chrisjtwomey/canary/include/display/notices/notice-no-firmware.png

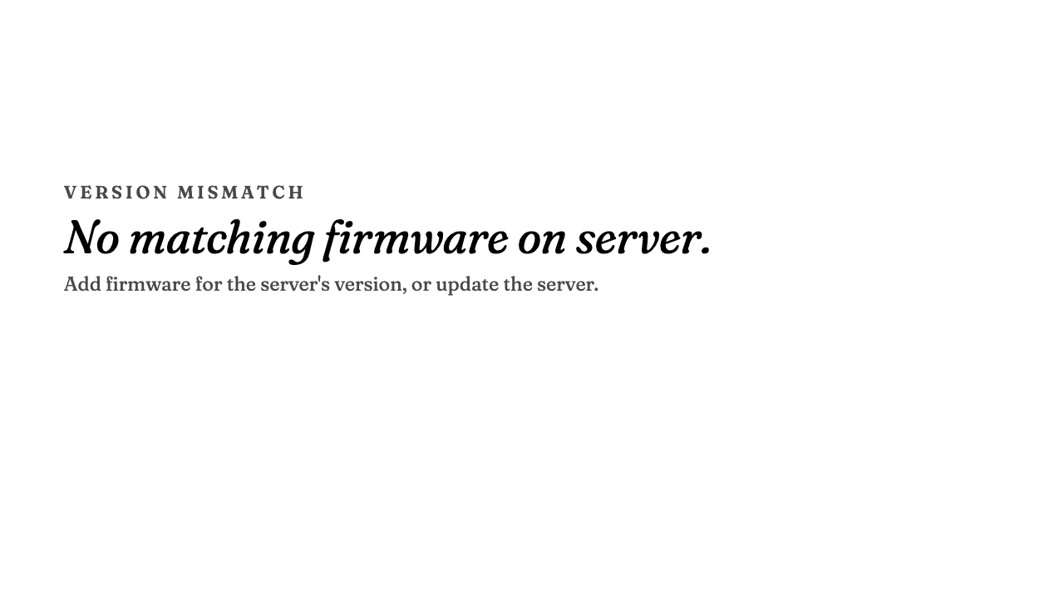
include/display/notices/notice-no-firmware.png
