chrisjtwomey/canary/server/config_page.py

"""config.yaml in the browser: a form in tabs, the file as text, a check, a
save and a restart.

    GET  /web/config     the form, and the file as text in the last tab
    GET  /web/config/export/<store>
                         everything one store holds, a JSON document a line
    POST /web/config/import/<store>
                         such a file back into that store, all of it or none;
                         replace=true puts it over the records that exist
    POST /web/config     mode=form: the form's values written into the file
                         mode=yaml: the text as given
                         mode=restore: config.yaml.bak
                         mode=recalibrate: the dock's SCD41 recalibrated to
                              ppm at its next reading; no action, no restart
                         then action=check: whether that would start the server
                              action=review: the same, and what it changes, as JSON
                              action=save: the same check, then the old file kept
                              as config.yaml.bak, the new one written, and the
                              server restarted on it; as JSON, with the
                              config_version /about names once it runs it

Nothing guards these routes yet: anyone who can reach the server can change
its config.
"""
from __future__ import annotations

import contextlib
import json
import os
import shutil
import time
import zoneinfo
from dataclasses import dataclass, field, replace
from datetime import datetime
from typing import Any, Callable

from airium import Airium
from epd_server.timeranges import MAX_RANGES
from flask import Blueprint, Response, abort, jsonify, redirect, request
from markupsafe import Markup

import config_form as cf
import dock_settings as ds
from about import config_version
from display_settings import DisplaySync
from html_doc import Html
from metrics import RH_BANDS, TEMP_BANDS, VERDICTS
from pages.base import EnvPage
from metrics import age_span
from transfer import Corrupt, Held, Overlap, Transfer
from web import menu_bar, page_head

# The most an imported file may weigh.
MAX_UPLOAD = 64 * 1024 * 1024
# The browse page's URL from /web/config, once the server answers again.
BROWSE_HREF = "./"
YAML_TAB = "yaml"
TAB_NAMES = [t.name for t in cf.TABS] + [YAML_TAB]

# What each drawing on a sheet shows, and how to change it by dragging.
VISUAL_CAPTIONS = {
    "dial": "Each tick is a sync. Hatching marks a time range that is off. "
            "Drag a time range's start to move it.",
    "panel": "Hatching shows where pages are drawn. "
             "Drag the round handle to resize it; click a dot to move it.",
    "slot": "The time before one sync. "
            "Drag the fan band's left edge; past the start, the fan never stops.",
    "start": "Each dot is a reading after the sensor starts; open dots have CO₂ only. "
             "Drag the band's edge to change the warm-up.",
    "comfort": "",
    "disk": "",
    "led": "What the light showed at the dock's last sync, until you change or click a "
           "pattern. Its size follows Brightness.",
}

# What a check or a save that changed nothing says, as a dialog's heading,
# its line, and whether it offers the save. Without scripts the note stays a
# banner.
NOTICES = {
    "No problems found.": ("No problems found", "Save and restart to apply these changes.",
                           True),
    "Nothing to save.": ("No changes", "The file already has these settings.", False),
}

# One wording for the state, whether it is a banner or a refused save.
READ_ONLY = "Cannot save: the server is missing write access to the configuration."


def save(path: str, text: str) -> str:
    """Keep ``path`` as it was beside it, then write ``text`` over it in place.
    Returns what it wrote: ``text`` ending in a newline.

    In place, because a file mounted into a container on its own cannot be
    replaced by a rename.
    """
    shutil.copyfile(path, path + ".bak")
    written = text if text.endswith("\n") else text + "\n"
    with open(path, "w") as f:
        f.write(written)
    return written


@dataclass
class Report:
    """What an import did, shown under the row that did it."""
    store: str = ""
    words: str = ""
    bad: bool = False


@dataclass
class View:
    """What the config page shows."""
    text: str                       # the YAML tab's text
    file_text: str                  # the file as it is
    values: dict[str, Any]          # each field as its input shows it
    initial: dict[str, Any]         # the same from the file: what a change is measured against
    defaults: dict[str, str] = field(default_factory=dict)   # each default, as its input shows it
    errors: dict[str, str] = field(default_factory=dict)
    problem: str = ""
    note: str = ""
    status: str = ""                # the save bar's words, when no note says more
    tab: str = ""                   # the tab to open; empty lets the URL choose
    unreadable: str = ""            # why the form cannot show this file
    held: dict[str, Held] = field(default_factory=dict)      # what each store holds
    now: float = 0.0                # the epoch the store ages are measured to
    disk: tuple[int, int] | None = None     # the stores' disk: total and free bytes
    report: Report = field(default_factory=Report)
    dock: DockState | None = None
    display: dict | None = None     # the display's panel as it reports it: width, height, board
    display_state: DisplayState | None = None
    changes: list[dict] = field(default_factory=list)   # what a check found a save would change


@dataclass
class DockState:
    """What the Dock tab says about the dock beside its settings."""
    applied: bool | None = None     # runs the saved settings; None before it says
    refused: list[str] = field(default_factory=list)
    pending: dict | None = None     # a recalibration it has yet to run
    last: dict | None = None        # its report of the last one it ran
    ppm: str = str(ds.RECALIBRATE_MIN_PPM + 20)
    offline: bool = False           # it has missed two slots; nothing on the tab reaches it
    age_s: int | None = None        # since its last sync
    expired: dict | None = None     # a recalibration that lapsed before the dock ran it
    next_sync: str = ""             # the local time of its next slot, HH:MM
    light: str | None = None        # what its light showed at its last report


def display_panel(entry: dict | None) -> dict | None:
    """The display's panel from its newest report: width, height and board, or
    None before it has said."""
    client = ((entry or {}).get("doc") or {}).get("client") or {}
    panel = client.get("display") or {}
    width, height = panel.get("width"), panel.get("height")
    if not isinstance(width, int) or not isinstance(height, int) or width <= 0 or height <= 0:
        return None
    return {"width": width, "height": height, "board": str(client.get("board") or "")}


@dataclass
class DisplayState:
    """What the Display tab says about the display beside its settings."""
    applied: bool | None = None     # runs the saved settings; None before it reports
    offline: bool = False           # it has missed two slots
    age_s: int | None = None        # since its last sync
    next_sync: str = ""             # the local time of its next slot, HH:MM


def display_state(display: DisplaySync) -> DisplayState:
    offline, age = display.offline()
    return DisplayState(display.applied(), offline, age, display.next_sync())


def dock_state(dock: ds.BoardSettings) -> DockState:
    applied, refused = dock.applied()
    offline, age = dock.offline()
    return DockState(applied, refused, dock.pending(), dock.last_recalibration(),
                     offline=offline, age_s=age, expired=dock.expired(),
                     next_sync=dock.next_sync(), light=dock.light())


def file_view(text: str) -> View:
    try:
        cfg = cf.read(text)
    except cf.FormError as exc:
        values = cf.shown({})
        return View(text, text, values, dict(values), tab=YAML_TAB,
                    unreadable=str(exc))
    values = cf.shown(cfg)
    return View(text, text, values, dict(values), cf.defaults(cfg))


def _id(key: str) -> str:
    return "f-" + key.replace(".", "-")


def _when(t: datetime) -> str:
    return f"{t:%a} {t.day} {t:%b}, {t:%H:%M}"


def _pool_names(view: View) -> list[str]:
    return [n for n, _ in view.values.get("display.pools", []) if n.strip()]


def _pool_row(a: Airium, key: str, name: str, pages: str, images: list[str]) -> None:
    with a.div(klass="row"):
        a.input(type="text", klass="pool-name", name=key + ".name", value=name,
                placeholder="name", spellcheck="false", autocomplete="off",
                **{"aria-label": "Set name"})
        a.input(type="text", klass="chips", name=key + ".pages", value=pages,
                spellcheck="false", autocomplete="off", placeholder="breathe.png, co2-trace.png",
                **{"aria-label": "Pages", "data-options": " ".join(images)})
        a.button(type="button", klass="remove", _t="×", **{"aria-label": "Remove this set"})


# A clock face in the ink of the button it is on.
CLOCK_ICON = Markup('<svg viewBox="0 0 16 16" aria-hidden="true">'
                    '<circle cx="8" cy="8" r="6.25" fill="none" stroke="currentColor" '
                    'stroke-width="1.5"/><path d="M8 4.5V8l2.25 1.5" fill="none" '
                    'stroke="currentColor" stroke-width="1.5" stroke-linecap="round" '
                    'stroke-linejoin="round"/></svg>')


def _time_input(a: Airium, **attrs) -> None:
    """A time input, and the button that opens the page's own picker
    (timepick.js): the browser's takes its colours from the system."""
    lock = {"disabled": "disabled"} if "disabled" in attrs else {}
    with a.span(klass="time"):
        a.input(type="time", **attrs)
        a.button(type="button", klass="pick", _t=CLOCK_ICON,
                 **{"aria-label": "Choose a time", "aria-expanded": "false"}, **lock)


def _clock_row(a: Airium, key: str, start: str, every: str, locked: bool) -> None:
    lock = {"disabled": "disabled"} if locked else {}
    with a.div(klass="row"):
        _time_input(a, name=key + ".from", value=start, **{"aria-label": "From"}, **lock)
        with a.span(klass="every"):
            a.input(type="number", name=key + ".every", value=every, min="0",
                    max=str(24 * 60), step="1", inputmode="numeric",
                    **{"aria-label": "Every, in minutes"}, **lock)
            a.span(klass="unit", _t="min")
        a.button(type="button", klass="remove", _t="×",
                 **{"aria-label": "Remove this time range; the one before takes its hours"},
                 **lock)


def _look_row(a: Airium, key: str, trigger: str, pattern: str, length: str,
              locked: bool) -> None:
    lock = {"disabled": "disabled"} if locked else {}
    with a.div(klass="row"):
        with a.select(name=key + ".trigger", **{"aria-label": "Trigger"}, **lock):
            for t, words in cf.LED_TRIGGER_LABELS.items():
                a.option(value=t, _t=words, **({"selected": "selected"} if t == trigger else {}))
        with a.select(name=key + ".pattern", **{"aria-label": "Pattern"}, **lock):
            for p, words in cf.LED_PATTERN_LABELS.items():
                a.option(value=p, _t=words, **({"selected": "selected"} if p == pattern else {}))
        # Off and solid keep their length, unseen, so each row posts all three.
        with a.span(klass="length idle" if pattern in ds.LED_STILL else "length"):
            a.input(type="number", name=key + ".length_s", value=length,
                    min=f"{ds.led_min_length(pattern):g}", max=f"{ds.LED_LENGTH_MAX_S:g}",
                    step="any", inputmode="decimal", **{"aria-label": "Length, in seconds"},
                    **lock)
            a.span(klass="unit", _t="s")
        a.button(type="button", klass="remove", _t="×",
                 **{"aria-label": "Remove this pattern; its trigger is skipped"}, **lock)


def _row(a: Airium, f: cf.Field, cells: tuple, images: list[str], locked: bool) -> None:
    if f.kind == "pools":
        _pool_row(a, f.key, *cells, images)
    else:
        _look_row(a, f.key, *cells, locked)


# What a new row starts as: a look takes its trigger's default once it has one.
BLANK_ROWS = {"looks": ("", "pulse", "1")}
# The words on each field's button that adds a row.
ADD_WORDS = {"pools": "Add a set", "looks": "Add a pattern"}


def _week(a: Airium, f: cf.Field, view: View, heading: str, locked: bool) -> None:
    """A schedule's groups of days, each with its time ranges. config.js
    shows one group at a time, chosen by its chip, with a toggle for each
    day; without it every group shows under the name of its days. A
    group's inputs are named ``<key>.<n>.``, n its place among the groups."""
    lock = {"disabled": "disabled"} if locked else {}
    with a.fieldset(klass="week", id=_id(f.key),
                    **{"data-key": f.key, "data-initial": cf.initial(view.initial[f.key])}):
        a.legend(klass="name hide" if f.label == heading else "name", _t=f.label)
        # With the rows locked, the key goes unposted and the file's value stands.
        a.input(type="hidden", name=f.key, value="1", **lock)
        a.div(klass="groups", role="group", _t="", **{"aria-label": "Groups of days"})
        for n, (days, rows) in enumerate(view.values.get(f.key, [])):
            prefix = f"{f.key}.{n}"
            chosen = days.split(",")
            with a.div(klass="group"):
                a.p(klass="group-name", _t=cf.days_words(chosen))
                with a.div(klass="days", role="group", **{"aria-label": "Days"}):
                    for d in cf.DAYS:
                        a.button(type="button", _t=cf.DAY_SHORT[d][0], **lock,
                                 **{"data-day": d, "aria-label": cf.DAY_LONG[d],
                                    "aria-pressed": "true" if d in chosen else "false"})
                a.input(type="hidden", name=prefix + ".days", value=days, **lock)
                with a.fieldset(klass="rows clock", **{"data-max": str(MAX_RANGES)}):
                    with a.div(klass="list"):
                        for start, every in rows:
                            _clock_row(a, prefix, start, every, locked)
                    with a.template():
                        _clock_row(a, prefix, "", "", locked)
                    with a.div(klass="foot"):
                        a.button(type="button", klass="add", _t="Add a time range", **lock)
        if f.help:
            a.p(klass="help", _t=f.help)


def _rows(a: Airium, f: cf.Field, view: View, images: list[str], heading: str,
          locked: bool = False) -> None:
    """A field of rows. ``locked`` applies to the Dock tab's rows, the only
    ones on a tab that locks."""
    if f.kind == "week":
        _week(a, f, view, heading, locked)
        return
    rows = view.values.get(f.key, [])
    marks: dict[str, str] = {}
    if f.kind == "looks":
        marks = {"data-looks": json.dumps({t: [p, f"{n:g}"] for t, p, n in ds.LED_LOOKS},
                                          separators=(",", ":")),
                 "data-min": json.dumps({p: f"{ds.led_min_length(p):g}" for p in ds.LED_PATTERNS
                                         if p not in ds.LED_STILL}, separators=(",", ":"))}
    with a.fieldset(klass=f"rows {f.kind}", id=_id(f.key),
                    **{"data-key": f.key, "data-initial": cf.initial(view.initial[f.key])},
                    **marks):
        a.legend(klass="name hide" if f.label == heading else "name", _t=f.label)
        # With the rows locked, the key goes unposted and the file's value stands.
        a.input(type="hidden", name=f.key, value="1", **({"disabled": "disabled"} if locked else {}))
        if f.kind == "looks":
            # The selects and inputs name themselves; these are for the eye.
            with a.div(klass="heads", **{"aria-hidden": "true"}):
                for words in ("Trigger", "Pattern", "Length"):
                    a.span(_t=words)
        with a.div(klass="list"):
            for cells in rows:
                _row(a, f, cells, images, locked)
        with a.template():
            _row(a, f, BLANK_ROWS.get(f.kind, ("", "")), images, locked)
        with a.div(klass="foot"):
            if f.kind in ADD_WORDS:
                a.button(type="button", klass="add", _t=ADD_WORDS[f.kind],
                         **({"disabled": "disabled"} if locked else {}))
            if f.help:
                a.p(klass="help", _t=f.help)


def _control(a: Airium, f: cf.Field, view: View, env: str | None, locked: bool,
             aria_label: str = "") -> None:
    value = view.values.get(f.key, "")
    if env is not None and f.scale != 1 and env.strip().isdigit():
        env = cf.input_text(f, int(env))
    lock = {"disabled": "disabled"} if env is not None or locked else {}
    marks = {"data-default": view.defaults[f.key]} if f.key in view.defaults else {}
    own = {"id": _id(f.key), "name": f.key, "data-key": f.key,
           "data-initial": cf.initial(view.initial.get(f.key, "")), **lock, **marks}
    with a.div(klass="control"):
        if f.kind == "choice":
            chosen = env if env is not None else value
            with a.div(klass="segments", role="radiogroup", id=_id(f.key),
                       **{"aria-labelledby": _id(f.key) + "-name", "data-key": f.key,
                          "data-initial": view.initial.get(f.key, "")}, **marks):
                for choice, words in f.choices:
                    with a.label():
                        a.input(type="radio", name=f.key, value=choice, **lock,
                                **({"checked": "checked"} if choice == chosen else {}))
                        a.span(_t=words)
        elif f.kind == "stops":
            # A slider that moves in the field's stops, with the chosen one's
            # name beside it; config.js keeps the name in step.
            chosen = env if env is not None else value
            words = dict(f.choices)
            a.input(type="range", klass="stops", min="1", max=str(len(f.choices)), step="1",
                    value=chosen, **own,
                    **{"data-words": json.dumps([w for _, w in f.choices], ensure_ascii=False),
                       "aria-valuetext": words.get(str(chosen), "")})
            a.span(klass="unit stop-words", _t=words.get(str(chosen), ""), **{"aria-hidden": "true"})
        elif f.kind in ("bool", "window"):
            on = (env or "").strip().lower() in ("1", "true", "yes", "on") if env is not None \
                else value == "true"
            a.input(type="hidden", name=f.key, value="false", **lock)
            a.input(type="checkbox", klass="switch", value="true", **own,
                    **({"checked": "checked"} if on else {}))
            a.span(klass="state", **{"aria-hidden": "true"})
        else:
            attrs: dict[str, Any] = {"value": env if env is not None else value}
            if aria_label:
                attrs["aria-label"] = aria_label
            if f.hint:
                attrs["placeholder"] = f.hint
            if f.kind in ("int", "number"):
                attrs.update(type="number", step=str(f.step) if f.kind == "int" else "any",
                             inputmode="numeric" if f.kind == "int" else "decimal")
                if f.minimum is not None:
                    attrs["min"] = f"{f.minimum:g}"
                if f.maximum is not None:
                    attrs["max"] = f"{f.maximum:g}"
            elif f.kind != "time":
                attrs.update(type="password" if f.kind == "password" else "text",
                             spellcheck="false", autocomplete="off")
                if f.kind == "zone":
                    attrs["list"] = "zones"
                if f.kind == "order":
                    attrs.update(klass="chips",
                                 **{"data-options": " ".join(_pool_names(view)),
                                    "data-options-from": "display.pools"})
            if f.kind == "time":
                _time_input(a, **own, **attrs)
            else:
                a.input(**own, **attrs)
            if f.unit:
                a.span(klass="unit", _t=f.unit)


def _reset_button(a: Airium, f: cf.Field, view: View) -> None:
    """Puts the default back; it shows once the value differs from it."""
    at_default = view.values.get(f.key) == view.defaults[f.key]
    a.button(type="button", klass="reset", _t="Reset",
             **{"aria-label": f"Reset {f.label}"}, **({"hidden": "hidden"} if at_default else {}))


def _field(a: Airium, f: cf.Field, view: View, images: list[str], heading: str,
           locked: bool = False, sheet: bool = False, by_position: bool = False) -> None:
    """One setting. ``locked`` shows it and keeps it from being changed, as
    an environment variable does, but leaves the file's value standing. On a
    ``sheet`` a dotted leader runs from its name to its value. ``by_position``
    marks a choice the group's position grid stands in for once scripts run."""
    env = f.env_value()
    error = view.errors.get(f.key)
    klass = "field by-position" if by_position else "field"
    if f.kind in cf.ROWS:
        klass += " wide"
    if error:
        klass += " invalid"
    with a.div(klass=klass, **{"data-field": f.key}, **({"data-when": f.when} if f.when else {})):
        if f.kind in cf.ROWS:
            _rows(a, f, view, images, heading, locked)
        else:
            with a.div(klass="head"):
                if f.kind == "choice":
                    a.span(klass="name", id=_id(f.key) + "-name", _t=f.label)
                else:
                    a.label(klass="name", for_=_id(f.key), _t=f.label)
                if f.key in view.defaults and env is None and not locked:
                    _reset_button(a, f, view)
                if f.kind == "password":
                    a.button(type="button", klass="reveal", _t="Show",
                             **{"aria-controls": _id(f.key)})
            if sheet:
                a.span(klass="leader", **{"aria-hidden": "true"})
            _control(a, f, view, env, locked)
        if f.help and f.kind not in cf.ROWS:
            a.p(klass="help", _t=f.help)
        if f.caution:
            # config.js shows it while the value is below data-below.
            shown = f.cautions(env if env is not None else view.values.get(f.key))
            a.p(klass="caution", _t=f.caution,
                **{"data-below": f"{f.recommended:g}"},
                **({"data-zero-means-always": "true"} if f.zero_means_always else {}),
                **({} if shown else {"hidden": "hidden"}))
        if env is not None:
            a.p(klass="env", _t=f"Set by the environment variable {f.env_name}")
        if error:
            a.p(klass="error", id="e-" + _id(f.key)[2:], _t=error)


# The comfort group's fields as ranges: a tab for temperature and one for
# humidity, each with the comfortable range and the acceptable one.
COMFORT_AXES = (("Temperature", "temp", "°C"), ("Humidity", "rh", "%"))
COMFORT_BOXES = (("Comfortable", ""), ("Acceptable", "acceptable_"))


def _comfort_ranges(a: Airium, g: cf.Group, view: View, locked: bool) -> None:
    """Each box's two edges on each axis as one range, under a tab per axis,
    and one reset for all eight. config.js runs the tabs, and shows the reset
    while any edge differs from its default. Without scripts both axes show,
    each under its name."""
    by_key = {f.key: f for f in g.fields}
    with a.div(klass="ranges"):
        with a.div(klass="subtabs", role="tablist", **{"aria-label": "Measurement"}):
            for i, (words, axis, _) in enumerate(COMFORT_AXES):
                a.button(type="button", role="tab", klass="subtab", id=f"comfort-tab-{axis}",
                         _t=words, **{"data-axis": axis, "aria-controls": f"comfort-{axis}",
                                      "aria-selected": "true" if i == 0 else "false"})
        for words, axis, unit in COMFORT_AXES:
            with a.div(klass="range-panel", id=f"comfort-{axis}", role="tabpanel",
                       **{"data-axis": axis, "aria-labelledby": f"comfort-tab-{axis}"}):
                a.p(klass="panel-name", _t=words)
                for box_words, prefix in COMFORT_BOXES:
                    with a.div(klass="range-row"):
                        a.span(klass="name", _t=box_words)
                        with a.div(klass="range"):
                            for n, end in enumerate(("from", "to")):
                                if n:
                                    a.span(klass="dash", _t="–")
                                f = by_key[f"comfort.{prefix}{axis}_{end}"]
                                error = view.errors.get(f.key)
                                with a.div(klass="field" + (" invalid" if error else ""),
                                           **{"data-field": f.key}):
                                    _control(a, replace(f, unit=""), view, f.env_value(), locked,
                                             aria_label=f.label)
                                    if error:
                                        a.p(klass="error", id="e-" + _id(f.key)[2:], _t=error)
                            a.span(klass="unit", _t=unit)
    at_default = all(view.values.get(f.key) == view.defaults.get(f.key) for f in g.fields)
    a.button(type="button", klass="reset-group", _t="Reset to defaults",
             **({"hidden": "hidden"} if at_default or locked else {}))


def _bytes(count: int) -> str:
    """"512 bytes", "64 kB", "3.1 MB", "412 GB": as sheet.js writes them."""
    if count < 1000:
        return f"{count} bytes"
    for unit, size in (("GB", 10**9), ("MB", 10**6)):
        if count >= size:
            n = count / size
            return f"{n:.0f} {unit}" if n >= 100 else f"{n:.1f}".removesuffix(".0") + f" {unit}"
    return f"{count / 1000:.0f} kB"


def _since(oldest: float, now: float) -> str:
    """"since 09:14" today, "since 3 Sep" this year, "since 3 Sep 2025" before."""
    t, today = datetime.fromtimestamp(oldest), datetime.fromtimestamp(now)
    if t.date() == today.date():
        return f"since {t:%H:%M}"
    return f"since {t.day} {t:%b}" + ("" if t.year == today.year else f" {t.year}")


def _contents_parts(held: Held, now: float) -> list[str]:
    """["48,210 records", "3.1 MB", "since 3 Sep"], or that there are none."""
    if not held.records:
        return ["No records yet."]
    parts = [f"{held.records:,} record{'' if held.records == 1 else 's'}", _bytes(held.size)]
    if held.oldest is not None:
        parts.append(_since(held.oldest, now))
    return parts


def _contents(a: Airium, store: str, view: View) -> None:
    """What the store's file holds, as a line of the sheet."""
    with a.div(klass="field contents", **{"data-contents": store}):
        with a.div(klass="head"):
            a.span(klass="name", _t="Contents")
        a.span(klass="leader", **{"aria-hidden": "true"})
        with a.div(klass="control"):
            # Each part in a span of its own, so a line breaks between them.
            with a.span(klass="value"):
                for i, part in enumerate(_contents_parts(view.held[store], view.now)):
                    if i:
                        a(" · ")
                    a.span(_t=part)


def _transfer(a: Airium, store: str, held: Held, report: Report) -> None:
    """The store's file out and back in, as two links under its heading;
    Download shows once the store holds a record. Upload's controls belong
    to the form beside the settings form, because a form cannot hold
    another. config.js hides the file input and Replace, and asks instead."""
    form = f"import-{store}"
    with a.div(klass="transfer", **{"data-import": store}):
        with a.p(klass="links"):
            a.a(klass="link", href=f"config/export/{store}", download="download",
                _t="Download", **{"data-export": store},
                **({} if held.records else {"hidden": "hidden"}))
            a.button(type="submit", klass="link", form=form, _t="Upload")
        with a.p(klass="pick"):
            a.input(type="file", id=f"file-{store}", name="file", form=form,
                    accept=".jsonl,application/x-ndjson", **{"aria-label": "File to upload"})
            with a.label(klass="over"):
                a.input(type="checkbox", name="replace", value="true", form=form)
                a.span(_t="Replace")
        if report.store == store:
            a.p(klass="report error" if report.bad else "report help", _t=report.words)


# Each store's name, as its group on the Storage tab heads it, in the tab's order.
STORE_NAMES = {g.store: g.heading for t in cf.TABS for g in t.groups if g.store}


def _disk_usage(stores: dict[str, Transfer]) -> tuple[int, int] | None:
    """The total and free bytes of the disk the first store's file is on;
    None without stores, or when the disk cannot be read."""
    for store in stores.values():
        try:
            usage = shutil.disk_usage(os.path.dirname(os.path.abspath(store.path)))
        except OSError:
            return None
        return usage.total, usage.free
    return None


def _disk_data(held: dict[str, Held], disk: tuple[int, int] | None) -> dict:
    """What the disk drawing draws: each store's name and bytes, and the
    disk's total and free bytes when they are known."""
    data: dict[str, Any] = {"stores": [{"name": name, "size": held[store].size}
                                       for store, name in STORE_NAMES.items() if store in held]}
    if disk is not None:
        data["total"], data["free"] = disk
    return data


# When each board takes new settings: the dock before the reading at its
# sync, the display in the answer to its sync.
TAKES = {"dock": "before its next sync", "display": "when it next syncs"}


def _settings_line(a: Airium, state: DockState | DisplayState, board: str) -> None:
    """Whether ``board`` runs the saved settings, as a banner across its tab:
    a pill naming the state, then what it means. config.js puts a new one in
    its place from GET /web/config/live."""
    last = Markup("Last sync {} ago.").format(age_span(state.age_s or 0))
    at = f", at {state.next_sync}" if state.next_sync else ""
    if state.offline and board == "dock":
        pill = ("offline", "Offline", last + " Settings unlock when the dock syncs again.")
    elif state.offline:
        pill = ("offline", "Offline", last + (" The display takes these settings when it "
                                              "syncs again." if state.applied is False else ""))
    elif state.applied is None:
        pill = None
    elif state.applied:
        pill = ("synced", "Synchronized", last)
    else:
        pill = ("waiting", "Not synchronized",
                f"The {board} takes these settings {TAKES[board]}{at}.")
    with a.div(klass="board-state", id=f"{board}-state",
               **{"data-offline": "true" if state.offline else "false"}):
        with a.p(klass="banner board-line", id=f"{board}-applied"):
            if pill is None:
                a.span(_t=f"No sync from the {board} yet. Settings apply once it connects.")
            else:
                klass, name, words = pill
                a.span(klass=f"pill {klass}", id=f"{board}-{klass}", _t=name)
                a.span(_t=words)
        if getattr(state, "refused", None):
            names = ", ".join(_label_of(("dock", *key.split("."))) for key in state.refused)
            a.p(klass="error", id="dock-refused",
                _t=f"Refused by the dock: {names}. Check the dock's firmware version.")


def _saved_words(states: dict[str, DockState | DisplayState | None]) -> str:
    """The save bar's words after a save: which board has yet to take the new
    settings, and when."""
    waiting = [(board, _takes_at(state)) for board, state in states.items()
               if state is not None and state.applied is False]
    if not waiting:
        return "Saved."
    (board, when), *rest = waiting
    return (f"Saved. The {board} takes the new settings {when}"
            + "".join(f", the {b} {w}" for b, w in rest) + ".")


def _takes_at(state: DockState | DisplayState) -> str:
    if state.offline:
        return "when it syncs again"
    return f"at {state.next_sync}" if state.next_sync else "at its next sync"


def _label_of(path: tuple) -> str:
    """A setting's name as its own tab shows it."""
    f = cf.field_at(path)
    return (f.long or f.label) if f else ".".join(path)


def _recalibration_words(state: DockState) -> str:
    if state.pending:
        asked = datetime.fromtimestamp(state.pending["id"])
        lapses = datetime.fromtimestamp(state.pending["id"] + ds.RECALIBRATE_WITHIN_S)
        return (f"Waiting for the dock's next sync: {state.pending['ppm']} ppm, "
                f"asked {_when(asked)}. Expires at {lapses:%H:%M}.")
    if state.expired:
        return (f"Recalibration to {state.expired['ppm']} ppm expired: "
                "the dock did not sync within an hour.")
    last = state.last
    if not last:
        return ("Keep the dock in air of a known CO₂ level for 3 minutes, then enter that level. "
                "Outdoor air is about 420 ppm.")
    asked = _when(datetime.fromtimestamp(last["id"]))
    if not last.get("ok"):
        return (f"Last recalibration failed: {last.get('ppm', '?')} ppm, asked {asked}. "
                "The sensor refused it. Try again after 3 minutes in that air.")
    correction = last.get("correction_ppm", 0)
    return (f"Last recalibration: {last.get('ppm', '?')} ppm, asked {asked}. "
            f"Corrected by {correction:+d} ppm.")


def _recalibrate(a: Airium, state: DockState, report: Report, sheet: bool = False) -> None:
    """The row that asks for a recalibration. Its controls belong to the form
    beside the settings form, as the import rows' do."""
    form = "recalibrate-form"
    lock = {"disabled": "disabled"} if state.offline else {}
    with a.div(klass="field wide", **{"data-recalibrate": "scd41"}):
        with a.div(klass="head"):
            a.label(klass="name", for_="recalibrate-ppm", _t="Recalibrate")
        if sheet:
            a.span(klass="leader", **{"aria-hidden": "true"})
        with a.div(klass="control"):
            a.input(type="number", id="recalibrate-ppm", name="ppm", form=form,
                    value=state.ppm, step="1", inputmode="numeric",
                    min=str(ds.RECALIBRATE_MIN_PPM), max=str(ds.RECALIBRATE_MAX_PPM), **lock)
            a.span(klass="unit", _t="ppm")
            a.button(type="submit", klass="button", form=form, _t="Recalibrate", **lock)
        if report.store == "recalibrate":
            a.p(klass="error" if report.bad else "help", _t=report.words)
        else:
            a.p(klass="help", id="recalibrate-state", _t=_recalibration_words(state))


def _changes_table(a: Airium, changes: list[dict]) -> None:
    """Each change as its setting, what it was and what it becomes."""
    with a.div(klass="changes-box"):
        with a.table(klass="changes"):
            with a.tbody():
                for c in changes:
                    with a.tr():
                        a.th(_t=c["name"])
                        a.td(klass="old", _t=c["old"])
                        a.td(klass="to", _t="→")
                        a.td(klass="new", _t=c["new"])


def _savebar(a: Airium, writable: bool, status: str, *, discard: bool) -> None:
    with a.footer(klass="savebar"):
        a.p(klass="status", _t=status, **{"aria-live": "polite",
                                          "data-idle": "No changes."})
        with a.div(klass="choice"):
            if discard:
                a.a(klass="button discard", href="config", _t="Discard")
            a.button(type="submit", name="action", value="check", _t="Check")
            a.button(type="submit", name="action", value="save", klass="primary",
                     _t="Save and restart", **({} if writable else {"disabled": "disabled"}))


@contextlib.contextmanager
def _nothing():
    yield


def _place_words(x: str, y: str) -> str:
    """"Top left", "Centre right", "Centre": a grid square's name."""
    across = {"left": "left", "center": "centre", "right": "right"}[x]
    down = {"top": "Top", "center": "Centre", "bottom": "Bottom"}[y]
    return "Centre" if x == y == "center" else f"{down} {across}"


def _position(a: Airium, g: cf.Group, view: View, locked: bool) -> None:
    """A 3 × 3 grid that sets the group's two alignments, across and up and
    down, with one click. It stands in for their two rows of choices, which
    stay in the form as what a save sends."""
    across, down = [f for f in g.fields if f.kind == "choice"]
    x = view.values.get(across.key) or "center"
    y = view.values.get(down.key) or "center"
    lock = {"disabled": "disabled"} if locked or across.env_value() or down.env_value() else {}
    with a.div(klass="field position"):
        with a.div(klass="head"):
            a.span(klass="name", id="position-name", _t="Position")
        a.span(klass="leader", **{"aria-hidden": "true"})
        with a.div(klass="control"):
            with a.div(klass="grid3", role="group",
                       **{"aria-labelledby": "position-name", "data-x": across.key,
                          "data-y": down.key}):
                for yv in ("top", "center", "bottom"):
                    for xv in ("left", "center", "right"):
                        a.button(type="button", _t="", **lock,
                                 **{"data-x": xv, "data-y": yv,
                                    "aria-label": _place_words(xv, yv),
                                    "aria-pressed": "true" if (xv, yv) == (x, y) else "false"})


def _display_size(a: Airium, view: View) -> None:
    """The size the display reports, against the saved one."""
    display = view.display
    if not display:
        return
    said = f"{display['width']} × {display['height']} px"
    if display.get("board"):
        said += f", {display['board']}"
    try:
        saved = (int(view.initial["image.width"]), int(view.initial["image.height"]))
    except (KeyError, ValueError):
        saved = None
    if saved == (display["width"], display["height"]):
        a.p(klass="help display-size", id="display-size", _t=f"The display reports {said}.")
    else:
        a.p(klass="error display-size", id="display-size",
            _t=f"Size mismatch: the display reports {said}. Set Width and Height to match.")


def _runs(fields: tuple[cf.Field, ...], sheet: bool) -> list[tuple[str, list[cf.Field]]]:
    """The fields in order, those in a row that show only while another field
    holds a value run together under that ``when``, on a sheet, so two or
    more can share one box. Elsewhere each field stands alone."""
    runs: list[tuple[str, list[cf.Field]]] = []
    for f in fields:
        when = f.when if sheet else ""
        if when and runs and runs[-1][0] == when:
            runs[-1][1].append(f)
        else:
            runs.append((when, [f]))
    return runs


def _group(a: Airium, g: cf.Group, view: View, images: list[str], locked: bool,
           sheet: bool = False) -> None:
    """A group's heading, the line under it that says what the group is for,
    and its fields. On a ``sheet`` a heading such as "CO₂ · SCD41" takes two
    lines, the part under the measurement, the heading and its line keep to
    their column, and the group's drawing, when it has one, comes before its
    fields."""
    stored = g.store in view.held
    with a.div(klass="heading") if sheet else _nothing():
        if g.heading and sheet and " · " in g.heading:
            title, part = g.heading.split(" · ", 1)
            with a.h2(klass="group label"):
                a.span(_t=title)
                a.span(klass="part", _t=part)
        elif g.heading:
            a.h2(klass="group label", _t=g.heading)
        if g.heading and g.about:
            a.p(klass="about", _t=g.about)
        if stored:
            _transfer(a, g.store, view.held[g.store], view.report)
    with a.div(klass=f"content visual-{g.visual}" if g.visual else "content") if sheet \
            else _nothing():
        if sheet and g.visual:
            # A dial draws the schedule its group holds.
            key = next((f.key for f in g.fields if f.kind == "week"), "")
            marks = {"data-schedule": key} if key else {}
            rec = next((f.recommended for f in g.fields if f.recommended is not None), None)
            if rec is not None:
                marks["data-recommended"] = f"{rec:g}"
            if g.visual == "disk":
                marks["data-disk"] = json.dumps(_disk_data(view.held, view.disk),
                                                separators=(",", ":"))
            if g.visual == "comfort":
                # The Comfort page's sentences, so the live text says what it would.
                marks["data-verdicts"] = json.dumps(
                    {"temp": TEMP_BANDS, "rh": RH_BANDS, "words": VERDICTS},
                    separators=(",", ":"))
            with a.div(klass="visual"):
                if g.visual == "led":
                    # A dot sheet.js lights as the dock would, and the look it plays:
                    # what the light showed at the dock's last report, until a row is picked.
                    light = view.dock.light if view.dock and not view.dock.offline else None
                    with a.div(klass="led-preview", id="visual-led", **{"data-visual": "led"},
                               **({"data-light": light} if light else {})):
                        a.span(klass="dot", **{"aria-hidden": "true"})
                        a.span(klass="led-look", _t="", **{"aria-live": "polite"})
                else:
                    a.canvas(id="-".join(["visual", g.visual, *key.split(".")]) if key
                             else f"visual-{g.visual}",
                             **{"data-visual": g.visual, "aria-hidden": "true"}, **marks)
                    if g.visual == "comfort":
                        # The room now, and its words with the boxes as drawn; sheet.js fills it.
                        with a.div(klass="comfort-now", id="comfort-now", **{"aria-live": "polite"}):
                            with a.div(klass="now-line"):
                                a.span(klass="now-temp", _t="—")
                                a.span(klass="unit", _t="°C")
                            with a.div(klass="now-line"):
                                a.span(klass="now-rh", _t="—")
                                a.span(klass="unit", _t="%")
                            a.div(klass="verdict", _t="")
                caption = g.caption or VISUAL_CAPTIONS[g.visual]
                if caption:
                    a.p(klass="caption", _t=caption)
        with a.div(klass="fields"):
            if stored:
                _contents(a, g.store, view)
            if g.visual == "comfort":
                _comfort_ranges(a, g, view, locked)
            for when, fields in [] if g.visual == "comfort" else _runs(g.fields, sheet):
                boxed = when and len(fields) > 1
                with a.div(klass="subsection", **{"data-when": when}) if boxed else _nothing():
                    for f in fields:
                        _field(a, f, view, images, g.heading, locked, sheet,
                               by_position=g.action == "position" and f.kind == "choice")
            if g.action == "position":
                _position(a, g, view, locked)
            if g.action == "display":
                _display_size(a, view)
            if g.action == "recalibrate" and view.dock is not None:
                _recalibrate(a, view.dock, view.report, sheet)


def _tab_problems(view: View) -> set[str]:
    tabs = {cf.TAB_OF[k] for k in view.errors if k in cf.TAB_OF}
    if view.problem and view.tab and view.tab != YAML_TAB:
        tabs.add(view.tab)
    return tabs


def config_html(pages: list[EnvPage], view: View, writable: bool,
                bak: datetime | None = None) -> str:
    images = [p.png_filename for p in pages]
    tabs = [] if view.unreadable else [(t.name, t.title) for t in cf.TABS]
    tabs.append((YAML_TAB, "YAML"))
    marked = _tab_problems(view)
    status = view.note or view.status or (
        "Not saved. Fix the marked fields." if view.errors
        else "Not saved." if view.problem else "No changes.")
    a = Html()
    a("<!DOCTYPE html>")
    with a.html(lang="en"):
        page_head(a, "Canary · Settings")
        with a.body(klass="web config"):
            menu_bar(a, pages, BROWSE_HREF, "config")
            with a.main(klass="settings"):
                with a.div(klass="top"):
                    a.h1(klass="title label", _t="Settings")
                    with a.div(klass="where"):
                        if bak is not None and writable:
                            with a.form(method="post", action="config", klass="restore",
                                        id="restore-form",
                                        **{"data-title": "Restore the previous version?",
                                           "data-confirm": "Restore and restart"}):
                                a.input(type="hidden", name="mode", value="restore")
                                a.span(klass="stamp", _t=f"Last saved {_when(bak)}")
                                a.button(type="submit", name="action", value="save",
                                         klass="link", _t="Restore")
                with a.nav(klass="tabs", role="tablist", **{"aria-label": "Sections"},
                           **({"data-open": view.tab} if view.tab else {})):
                    for name, title in tabs:
                        a.a(href=f"#{name}", id=f"tab-{name}", role="tab",
                            klass="tab problem" if name in marked else "tab",
                            _t=title, **{"data-tab": name, "aria-controls": f"panel-{name}"})
                if not writable:
                    a.p(klass="banner", id="read-only",
                        _t=READ_ONLY)
                if view.unreadable:
                    a.p(klass="banner problem", id="unreadable", _t=view.unreadable)
                if view.problem:
                    a.p(klass="banner problem", id="problem", _t=f"Not saved: {view.problem}")
                if view.note:
                    a.p(klass="banner", id="note", _t=view.note)
                if not view.unreadable:
                    with a.form(method="post", action="config", id="settings-form",
                                novalidate="novalidate",
                                **{"data-title": "Save and restart?",
                                   "data-confirm": "Save and restart"}):
                        a.input(type="hidden", name="mode", value="form")
                        a.input(type="hidden", name="tab", value=view.tab or cf.TABS[0].name)
                        for t in cf.TABS:
                            with a.section(klass="panel sheet" if t.sheet else "panel",
                                           id=f"panel-{t.name}", role="tabpanel",
                                           **{"data-tab": t.name,
                                              "aria-labelledby": f"tab-{t.name}"}):
                                locked = False
                                if t.name == "dock" and view.dock is not None:
                                    _settings_line(a, view.dock, "dock")
                                    locked = view.dock.offline
                                if t.name == "display" and view.display_state is not None:
                                    _settings_line(a, view.display_state, "display")
                                for g in t.groups:
                                    if t.sheet:
                                        with a.div(klass="section"):
                                            _group(a, g, view, images, locked, sheet=True)
                                    else:
                                        _group(a, g, view, images, locked)
                        _savebar(a, writable, status, discard=True)
                    for store in view.held:
                        a.form(method="post", action=f"config/import/{store}",
                               enctype="multipart/form-data", id=f"import-{store}")
                    if view.dock is not None:
                        with a.form(method="post", action="config", id="recalibrate-form"):
                            a.input(type="hidden", name="mode", value="recalibrate")
                with a.form(method="post", action="config", id="yaml-form",
                            **{"data-title": "Save and restart?",
                               "data-confirm": "Save and restart"}):
                    a.input(type="hidden", name="mode", value="yaml")
                    a.input(type="hidden", name="tab", value=YAML_TAB)
                    with a.section(klass="panel", id=f"panel-{YAML_TAB}", role="tabpanel",
                                   **{"data-tab": YAML_TAB, "aria-labelledby": f"tab-{YAML_TAB}"}):
                        a.textarea(name="text", rows="24", spellcheck="false", _t=view.text,
                                   **{"aria-label": "config.yaml", "data-key": "text",
                                      "data-initial": view.file_text})
                        _savebar(a, writable, status, discard=True)
            with a.dialog(id="review", **{"aria-labelledby": "review-title"}):
                with a.form(method="dialog"):
                    a.h2(klass="label", id="review-title", _t="Save and restart?")
                    a.p(klass="lead", id="review-lead")
                    with a.div(klass="changes-box"):
                        with a.table(klass="changes"):
                            a.tbody(id="review-list", _t="")
                    with a.div(klass="choice"):
                        a.button(value="cancel", _t="Cancel")
                        a.button(value="confirm", klass="primary", id="review-confirm",
                                 _t="Save and restart")
            if view.note in NOTICES:
                title, lead, offers_save = NOTICES[view.note]
                with a.dialog(id="notice", **{"aria-labelledby": "notice-title"},
                              **({"klass": "with-changes"} if view.changes else {})):
                    with a.form(method="dialog"):
                        a.h2(klass="label", id="notice-title", _t=title)
                        a.p(klass="lead", _t=lead)
                        if view.changes:
                            _changes_table(a, view.changes)
                        with a.div(klass="choice"):
                            a.button(value="close", autofocus="autofocus", _t="Close",
                                     **({} if offers_save else {"klass": "primary"}))
                            if offers_save:
                                a.button(value="save", klass="primary", _t="Save and restart",
                                         **({} if writable else {"disabled": "disabled"}))
            with a.datalist(id="zones"):
                for zone in sorted(zoneinfo.available_timezones()):
                    a.option(value=zone)
            a.script(src="rough.iife.min.js")
            a.script(src="config.js")
            a.script(src="timepick.js")
            a.script(src="sheet.js")
            a.script(src="ago.js")
    return str(a)


def restarting_html(pages: list[EnvPage], tab: str) -> str:
    """The page a save without config.js gets: it opens the config page
    again after a minute, once the server is back."""
    a = Html()
    a("<!DOCTYPE html>")
    with a.html(lang="en"):
        page_head(a, "Canary · Restarting", refresh=f"60; url=config?saved=1#{tab}")
        with a.body(klass="web config"):
            menu_bar(a, pages, BROWSE_HREF, "config")
            with a.main(klass="settings"):
                a.h1(klass="title label", _t="Settings")
                a.p(klass="banner", id="restarting", _t="Restarting…")
    return str(a)


def config_blueprint(pages: list[EnvPage], path: str, check: Callable[[str], None],
                     restart: Callable[[], None],
                     stores: dict[str, Transfer] | None = None,
                     dock: ds.BoardSettings | None = None,
                     display: DisplaySync | None = None,
                     boards: Callable[[str], dict | None] | None = None,
                     take_network: Callable[[str], None] | None = None) -> Blueprint:
    """The /web/config routes for the file at ``path``.

    Args:
        check: raises ValueError, with the problem, unless the text would
            start the server.
        restart: restarts the server once the response has gone out.
        stores: the store behind each group of the Storage tab that a file
            can come out of and go into, by the group's ``store`` name.
        dock: the dock's settings, for what the Dock tab says of them and
            for its recalibration.
        display: whether the display runs the saved settings, for what the
            Display tab says of them.
        boards: what the server knows of a board, as DeviceReports.device
            gives it, for the size the display reports.
        take_network: takes a saved file whose changes are all to the
            install page's settings, in place of a restart: they change only
            what an install writes, so the server can take them as it runs.
    """
    bp = Blueprint("config", __name__, url_prefix="/web/config")
    stores = stores or {}

    @bp.record_once
    def cap_uploads(state):
        state.app.config.setdefault("MAX_CONTENT_LENGTH", MAX_UPLOAD)

    def writable() -> bool:
        return os.access(path, os.W_OK)

    def bak() -> datetime | None:
        try:
            return datetime.fromtimestamp(os.path.getmtime(path + ".bak"))
        except OSError:
            return None

    def board_states(view: View) -> None:
        if dock is not None and view.dock is None:
            view.dock = dock_state(dock)
        if display is not None and view.display_state is None:
            view.display_state = display_state(display)

    def page(view: View, status: int = 200):
        view.held = {name: store.held() for name, store in stores.items()}
        view.now = time.time()
        view.disk = _disk_usage(stores)
        board_states(view)
        if boards is not None:
            view.display = display_panel(boards("canary-display"))
        return config_html(pages, view, writable(), bak()), status

    @bp.route("/live", methods=["GET"])
    def live():
        """The Dock and Display tabs' lines about each board as it is now,
        for config.js."""
        if dock is None and display is None:
            abort(404)
        answer: dict[str, Any] = {}
        if dock is not None:
            state = dock_state(dock)
            a = Html()
            _settings_line(a, state, "dock")
            answer.update(state=str(a), recalibration=_recalibration_words(state),
                          offline=state.offline, light=state.light)
        if display is not None:
            a = Html()
            _settings_line(a, display_state(display), "display")
            answer["display"] = str(a)
        return jsonify(answer)

    @bp.route("/export/<name>", methods=["GET"])
    def export(name: str):
        store = stores.get(name)
        if store is None:
            abort(404)
        stamp = datetime.now().strftime("%Y%m%d")
        return Response(store.lines(), mimetype="application/x-ndjson", headers={
            "Content-Disposition": f'attachment; filename="{name}-{stamp}.jsonl"'})

    @bp.route("/import/<name>", methods=["POST"])
    def bring_in(name: str):
        store = stores.get(name)
        if store is None:
            abort(404)
        as_json = "application/json" in request.headers.get("Accept", "")

        def answer(words: str, status: int = 200, bad: bool = False, advice: str = "",
                   **counts):
            """The answer as JSON, or the page with it under the import row.
            ``advice`` is for the page alone: with config.js a dialog asks."""
            if as_json:
                return jsonify(words=words, bad=bad, **counts), status
            with open(path) as f:
                view = file_view(f.read())
            view.tab = "storage"
            view.report = Report(name, " ".join(filter(None, (words, advice))), bad)
            return page(view, status)

        upload = request.files.get("file")
        if upload is None or not upload.filename:
            return answer("Choose a file to upload.", 400, bad=True)
        try:
            counts = store.take(upload.stream, request.form.get("replace") == "true")
        except Corrupt as exc:
            return answer(f"Upload failed: line {exc.line} is not a record. Check the file.",
                          400, bad=True)
        except Overlap as exc:
            return answer(f"{exc.held:,} of {exc.total:,} records already exist.",
                          409, bad=True, held=exc.held, total=exc.total,
                          advice="Tick Replace and choose the file again.")
        except FileNotFoundError:
            return answer("This server does not keep those records.", 404, bad=True)
        held = {n: s.held() for n, s in stores.items()}
        words = f"Added {counts['added']:,} of {counts['total']:,} records."
        if counts["held"]:
            words += f" {counts['held']:,} replaced."
        return answer(words, contents=_contents_parts(held[name], time.time()),
                      records=held[name].records, disk=_disk_data(held, _disk_usage(stores)),
                      **counts)

    @bp.errorhandler(413)
    def too_big(exc):
        words = f"File too big. Choose one under {MAX_UPLOAD // (1024 * 1024)} MB."
        if "application/json" in request.headers.get("Accept", ""):
            return jsonify(words=words, bad=True), 413
        with open(path) as f:
            view = file_view(f.read())
        view.tab = "storage"
        view.report = Report((request.view_args or {}).get("name", ""), words, True)
        return page(view, 413)

    @bp.route("", methods=["GET"])
    def show():
        with open(path) as f:
            view = file_view(f.read())
        if request.args.get("saved"):
            board_states(view)
            view.status = _saved_words({"dock": view.dock, "display": view.display_state})
        return page(view)

    @bp.route("", methods=["POST"])
    def change():
        form = request.form
        mode = form.get("mode") or ("yaml" if "text" in form else "form")
        action = form.get("action", "check")
        with open(path) as f:
            current = f.read()
        view = file_view(current)
        view.tab = form.get("tab", "") if form.get("tab") in TAB_NAMES else ""

        wants_json = action == "review" or "application/json" in request.headers.get("Accept", "")

        def refuse(problem: str, status: int = 400, key: str | None = None):
            if wants_json:
                at = {"field": key, "error": view.errors[key]} if key in view.errors else {}
                return jsonify(problem=problem, **at), status
            view.problem = problem
            return page(view, status)

        if mode == "recalibrate":
            if dock is None:
                abort(404)
            ppm = form.get("ppm", "")
            try:
                dock.recalibrate(ppm)
            except ValueError as exc:
                view.tab = "dock"
                view.dock = dock_state(dock)
                view.dock.ppm = ppm
                view.report = Report("recalibrate", str(exc), True)
                return page(view, 400)
            return redirect("config#dock", 303)

        if mode == "restore":
            try:
                with open(path + ".bak") as f:
                    text = f.read()
            except OSError:
                return refuse("No earlier version to restore.", 404)
        elif mode == "yaml":
            # A text box sends its lines with CRLF.
            text = form.get("text", "").replace("\r\n", "\n")
            view.text, view.tab = text, YAML_TAB
        else:
            view.values.update(cf.submitted(form))
            try:
                edit = cf.apply(current, form)
            except cf.FormError as exc:
                return refuse(str(exc))
            if edit.errors:
                view.errors = edit.errors
                key = next(f.key for f in cf.FIELDS if f.key in edit.errors)
                view.tab = cf.TAB_OF.get(key, view.tab)
                return refuse(f"{cf.name_of(cf.BY_KEY[key].path)}: {edit.errors[key]}", key=key)
            text = edit.text

        try:
            check(text)
        except ValueError as exc:
            problem = str(exc)
            if mode == "form":
                key, tab = cf.locate(problem)
                if key:
                    f = cf.BY_KEY[key]
                    if f.refused:
                        problem = f"{cf.name_of(f.path)}: {f.refused}"
                    view.errors[key] = f.refused or problem
                view.tab = tab or view.tab
                return refuse(problem, key=key)
            return refuse(problem)

        if action == "review":
            return jsonify(changes=cf.changes(cf.read(current), cf.read(text)),
                           same=text == current)
        if action != "save":
            if text == current:
                view.note = "Nothing to save."
            else:
                view.note = "No problems found."
                view.changes = cf.changes(cf.read(current), cf.read(text))
            return page(view)
        if text == current:
            if wants_json:
                return jsonify(saved=False, same=True)
            view.note = "Nothing to save."
            return page(view)
        if not writable():
            return refuse(READ_ONLY, 403)
        try:
            written = save(path, text)
        except OSError as exc:
            return refuse(f"Save failed: {exc.strerror}.", 500)
        if take_network is not None and mode == "form" and set(edit.changed) <= cf.INSTALL_KEYS:
            take_network(written)
            if wants_json:
                return jsonify(saved=True, config=config_version(written), restarted=False)
            return redirect("install", 303)
        restart()
        if wants_json:
            return jsonify(saved=True, config=config_version(written))
        return restarting_html(pages, view.tab or cf.TABS[0].name)

    return bp
