chrisjtwomey/canary/src/splash.cpp

#include "display/Splash.h"

#include <Arduino.h>

#include "epd.h"
#include "display/Notice.h"
#include "display/ProgressBar.h"
#include "display/fonts/FrauncesDetail.h"
#include "display/fonts/FrauncesDetailItalic.h"
#include "log_utils.h"
#include "version.h"

// The splash screen the server's pipeline rendered in black and white
// (scripts/notices.py), held in the firmware (board_build.embed_files).
extern const uint8_t splashPng[] asm("_binary_include_display_splash_png_start");
extern const uint8_t splashPngEnd[] asm("_binary_include_display_splash_png_end");

// The bar on the Inkplate 5's 1280 x 720, centred under the logo. The page
// sets the logo 60cqw wide in the middle of the panel (styles.css), so its
// lowest ink is at y 488.
static const int16_t kWidth = 1280;
static const int16_t kBarW = 512;
static const int16_t kBarH = 24;
static const int16_t kBarX = (kWidth - kBarW) / 2;
static const int16_t kBarY = 552;
static const int16_t kLine = 3;   // the outline
static const int16_t kGap = 4;    // between the outline and the fill
static const int16_t kFillX = kBarX + kLine + kGap;
static const int16_t kFillY = kBarY + kLine + kGap;
static const int16_t kFillW = kBarW - 2 * (kLine + kGap);
static const int16_t kFillH = kBarH - 2 * (kLine + kGap);
// The baselines of the lines the display writes, in the pages' face at the size
// of their detail text: the update's line under the bar, and the start's
// version where the bar would be.
static const int16_t kLineY = 622;
static const int16_t kVersionY = 572;

// In black and white.
static const uint16_t kBlack = 1;
static const uint16_t kWhite = 0;

static ProgressBar bar;
static char offeredVersion[32] = "";

// Into the frame buffer, in black and white; the caller pushes it.
static void drawLogo() {
    IBoard& board = epdBoard();
    board.setBlackAndWhite(true);
    board.clearDisplay();
    if (!board.drawPngFromBuffer((uint8_t*)splashPng, (int32_t)(splashPngEnd - splashPng), 0, 0, false, false))
        log(LOG_ERROR, "the splash image would not decode");
    noticeReplaced();
}

// Centred on the panel.
static void writeLine(const char* line, const GFXfont* font, int16_t baseline) {
    IBoard& board = epdBoard();
    board.setFont(font);
    board.setTextSize(1);
    board.setTextWrap(false);
    board.setTextColor(kBlack);
    int16_t x, y;
    uint16_t w, h;
    board.getTextBounds(line, 0, baseline, &x, &y, &w, &h);
    board.setCursor((kWidth - (int16_t)w) / 2 - x, baseline);
    board.print(line);
}

static void fillBar(int steps) {
    const int16_t w = kFillW * steps / ProgressBar::kSteps;
    if (w > 0) epdBoard().fillRect(kFillX, kFillY, w, kFillH, kBlack);
}

void showSplash() {
    drawLogo();
    writeLine(CLIENT_VERSION, &FrauncesDetail, kVersionY);
    epdBoard().display();
    epdBoard().setBlackAndWhite(false);
}

void showUpdateProgress(int done, int total) {
    IBoard& board = epdBoard();
    switch (bar.update(done, total)) {
        case ProgressBar::FULL:
            drawLogo();
            board.fillRect(kBarX, kBarY, kBarW, kBarH, kBlack);
            board.fillRect(kBarX + kLine, kBarY + kLine, kBarW - 2 * kLine, kBarH - 2 * kLine, kWhite);
            fillBar(bar.filled);
            char line[64];
            snprintf(line, sizeof(line), "Installing firmware %s...", offeredVersion);
            writeLine(line, &FrauncesDetailItalic, kLineY);
            board.display();
            break;
        case ProgressBar::PARTIAL:
            fillBar(bar.filled);
            board.partialDisplay();
            break;
        case ProgressBar::NONE:
            break;
    }
}

void beginUpdateProgress(const char* offered) {
    bar = ProgressBar{};
    strlcpy(offeredVersion, offered, sizeof(offeredVersion));
}

void endUpdateProgress() {
    epdBoard().setBlackAndWhite(false);
}
