chrisjtwomey/canary/include/sensors/Readings.h

#pragma once
#include <cstddef>
#include <cstdint>

// What each sensor hands back, and the set the firmware posts.
// Units and key names follow docs/readings.md.

struct Shtc3Data {
    float tempC;
    float rhPct;
};

struct Scd41Data {
    uint16_t co2Ppm;
    float    tempC;   // runs ~4 C warm until the offset is tuned
    float    rhPct;
};

struct PmData {
    uint16_t pm1_0Cf1, pm2_5Cf1, pm10Cf1;     // "CF=1, standard particle"
    uint16_t pm1_0, pm2_5, pm10;              // "atmospheric environment" — the ones we use
    uint16_t pc0_3, pc0_5, pc1_0, pc2_5, pc5_0, pc10;   // particles per 0.1 L
    uint8_t  version;
    uint8_t  error;
};

struct Bme688Data {
    float    tempC;        // runs warm; BSEC-internal
    float    pressureHpa;
    float    rhPct;
    float    gasOhm;
    bool     gasValid;     // a real gas conversion took place
    bool     heatStable;   // the heater reached its target; gasOhm is trustworthy only if true
    float    iaq;          // 0–500, when hasIaq
    uint8_t  iaqAccuracy;  // 0–3, when hasIaq
    bool     hasIaq;       // the index came with this reading; false without BSEC
    // BSEC's static index, which Bosch recommends for a device that stays in
    // one place: it does not stretch its scale to the last few days' air.
    float    staticIaq;          // 0–500, when hasStaticIaq
    uint8_t  staticIaqAccuracy;  // 0–3, when hasStaticIaq
    bool     hasStaticIaq;
};

struct Readings {
    uint32_t   ts;
    Shtc3Data  shtc3;   bool shtc3Valid;
    Scd41Data  scd41;   bool scd41Valid;
    // The SCD41's own temperature and humidity are to be kept. False during
    // its warm-up after a start; its CO2 is good from the first reading.
    bool       scd41WarmedUp;
    PmData     pm;      bool pmValid;
    Bme688Data bme688;  bool bme688Valid;
    // How long the PM fan had run when the particle reading was taken, in
    // seconds; 0 when nobody measured it.
    uint16_t   pmWarmupS;
    // How many samples each mean holds, over the interval before ts: the
    // SCD41's CO2, the BME688's cycles, and of those the cycles each index
    // counted (Bme688Mean).
    uint16_t   scd41Samples;
    uint16_t   bme688Samples;
    uint16_t   iaqSamples;
    uint16_t   staticIaqSamples;
};

// Encode to the JSON in docs/readings.md. Returns the length written, or 0
// if the buffer is too small (nothing partial is left behind).
size_t readingsToJson(const Readings& r, const char* device, char* buf, size_t len);
