chrisjtwomey/canary/include/sensors/mock/MockShtc3.h

#pragma once
#include "../IShtc3.h"
#include "EnvModel.h"
#include "LaggedValue.h"

// Behaves like the datasheet says an SHTC3 does: 12.1 ms per normal
// measurement, 0.8 ms in low-power mode, NACKs when asleep, +-0.1 C /
// +-0.1 %RH repeatability (0.4 / 0.4 in low-power mode).
//
// The element trails the room by its response time. Electrically there is no
// warm-up at all - 240 us to idle and the first reading is valid - so this
// lag is the only settling it has.
class MockShtc3 : public IShtc3 {
public:
    explicit MockShtc3(EnvModel& room) : room_(room) {}

    bool begin(uint32_t nowMs) override;
    bool wakeup(uint32_t nowMs) override;
    bool sleep() override;
    bool measure(uint32_t nowMs, bool lowPower) override;
    bool read(uint32_t nowMs, Shtc3Data& out) override;
    uint16_t readId() override { return 0x0887; }

    bool asleep() const { return asleep_; }

    static const uint32_t kNormalMs   = 13;   // 12.1 ms max, rounded up
    static const uint32_t kLowPowerMs = 1;    // 0.8 ms max
    // tau63: humidity 8 s. Temperature is quoted as 5-30 s "depends on heat
    // conductivity of sensor substrate and design-in"; 15 s is mid-range and
    // wants revisiting once the enclosure exists.
    static constexpr float kTempTauS = 15.0f;
    static constexpr float kRhTauS = 8.0f;

private:
    EnvModel& room_;
    bool asleep_ = true;
    bool measuring_ = false;
    bool lowPower_ = false;
    uint32_t readyAtMs_ = 0;
    uint32_t wokeAtMs_ = 0;
    LaggedValue temp_{kTempTauS};
    LaggedValue rh_{kRhTauS};
};
