chrisjtwomey/canary/server/schedule.py

"""canary's schedules when config.yaml gives none. epd_server.timeranges
holds how a week of time ranges works."""
from epd_server.timeranges import DAYS

# The dock syncs every half hour from 01:00 to 07:00, and every five
# minutes the rest of the day, every day.
DEFAULT_DOCK_WEEK = [{"days": list(DAYS), "ranges": [{"from": "01:00", "every": 1800},
                                                     {"from": "07:00", "every": 300}]}]
# The display syncs every half hour, beside each page it fetches.
DEFAULT_DISPLAY_SYNC_S = 1800
# A page an hour, all day, every day.
DEFAULT_PAGE_WEEK = [{"days": list(DAYS), "ranges": [{"from": "00:00", "every": 3600}]}]
